starboundstitch/gpu-external-power-supply/firmware/src/navigation.rs

use embedded_graphics::prelude::Point;

#[derive(Default)]
pub struct Navigation {
    // x, y
    position: (i32, i32),
    mode: Mode,
}

// Implements navigation across the microcontroller for the user input
impl Navigation {
    const X_MAX: i32 = 2;
    const Y_MAX: i32 = 3;

    pub fn get_position(&self) -> (i32, i32) {
        self.position
    }

    pub fn get_point(&self) -> Point {
        translate_point(self.position)
    }

    pub fn move_left(&mut self) {
        if self.position.0 > 0 {
            self.position.0 -= 1;
        }
    }

    pub fn move_right(&mut self) {
        if self.position.0 < Self::X_MAX - 1 {
            self.position.0 += 1;
        }
    }

    pub fn move_up(&mut self) {
        if self.position.1 > 0 {
            self.position.1 -= 1;
        }
    }

    pub fn move_down(&mut self) {
        if self.position.1 < Self::Y_MAX - 1 {
            self.position.1 += 1;
        }
    }

    pub fn change_mode(&mut self) {
        match self.mode {
            Mode::Navigation => self.mode = Mode::Update,
            Mode::Update => self.mode = Mode::Navigation,
        }
    }

    pub fn get_mode(&self) -> &Mode {
        &self.mode
    }
}

pub enum Mode {
    Navigation,
    Update,
}

impl Default for Mode {
    fn default() -> Mode {
        Mode::Navigation
    }
}

#[derive(Default, bincode::Decode, bincode::Encode)]
pub struct Device {
    core: Channel,
    mem: Channel,
}

impl Device {
    pub fn core(&mut self) -> &mut Channel {
        &mut self.core
    }
    pub fn mem(&mut self) -> &mut Channel {
        &mut self.mem
    }
    pub fn store_value(&mut self, point: (i32, i32), val: f32) {
        let chan = match point {
            (0, _) => self.core(),
            (1, _) => self.mem(),
            (_, _) => return,
        };
        match point {
            (_, 0) => chan.set_voltage(val),
            (_, 1) => chan.set_current(val),
            (_, _) => (),
        };
    }
}

#[derive(Default, bincode::Decode, bincode::Encode)]
pub struct Channel {
    voltage: f32,
    voltage_setpoint: f32,
    current: f32,
    current_limit: f32,
    temperature: f32,
}

impl Channel {
    pub fn get_voltage(&self) -> f32 {
        self.voltage
    }
    pub fn set_voltage(&mut self, val: f32) {
        self.voltage = val;
    }
    pub fn get_voltage_setpoint(&self) -> f32 {
        self.voltage_setpoint
    }
    pub fn set_voltage_setpoint(&mut self, val: f32) {
        self.voltage_setpoint = val;
    }
    pub fn get_current(&self) -> f32 {
        self.current
    }
    pub fn set_current(&mut self, val: f32) {
        self.current = val;
    }
    pub fn get_current_limit(&self) -> f32 {
        self.current_limit
    }
    pub fn set_current_limit(&mut self, val: f32) {
        self.current_limit = val;
    }
    pub fn get_temperature(&self) -> f32 {
        self.temperature
    }
    pub fn set_temperature(&mut self, val: f32) {
        self.temperature = val;
    }
}

pub fn translate_point(point: (i32, i32)) -> Point {
    Point::new(27 + 6 * 9 * point.0, 16 + 16 * point.1)
}
